Mounith-H/AI-PEGD/images/accuracy_plot_400.png

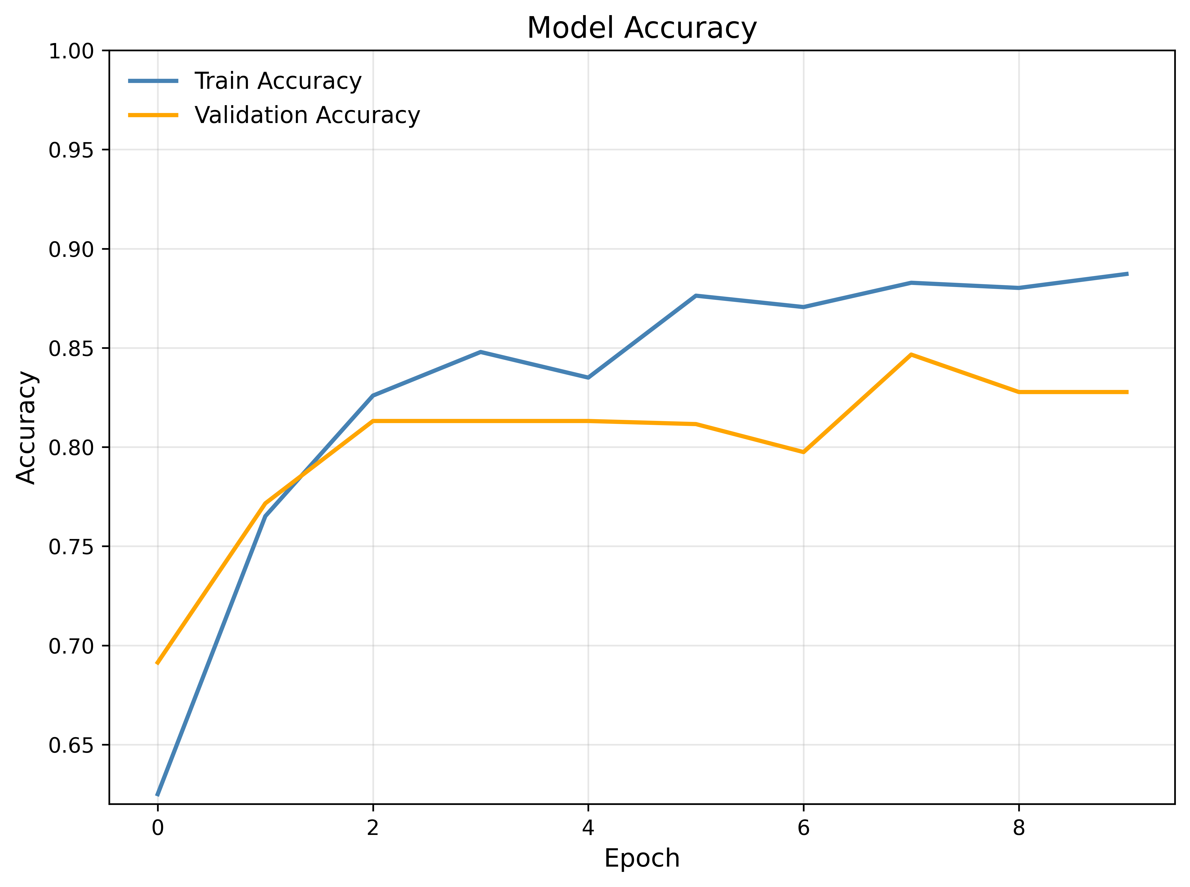
images/accuracy_plot_400.png
