Mounith-H/AI-PEGD/images/accuracy_plot_1000.png

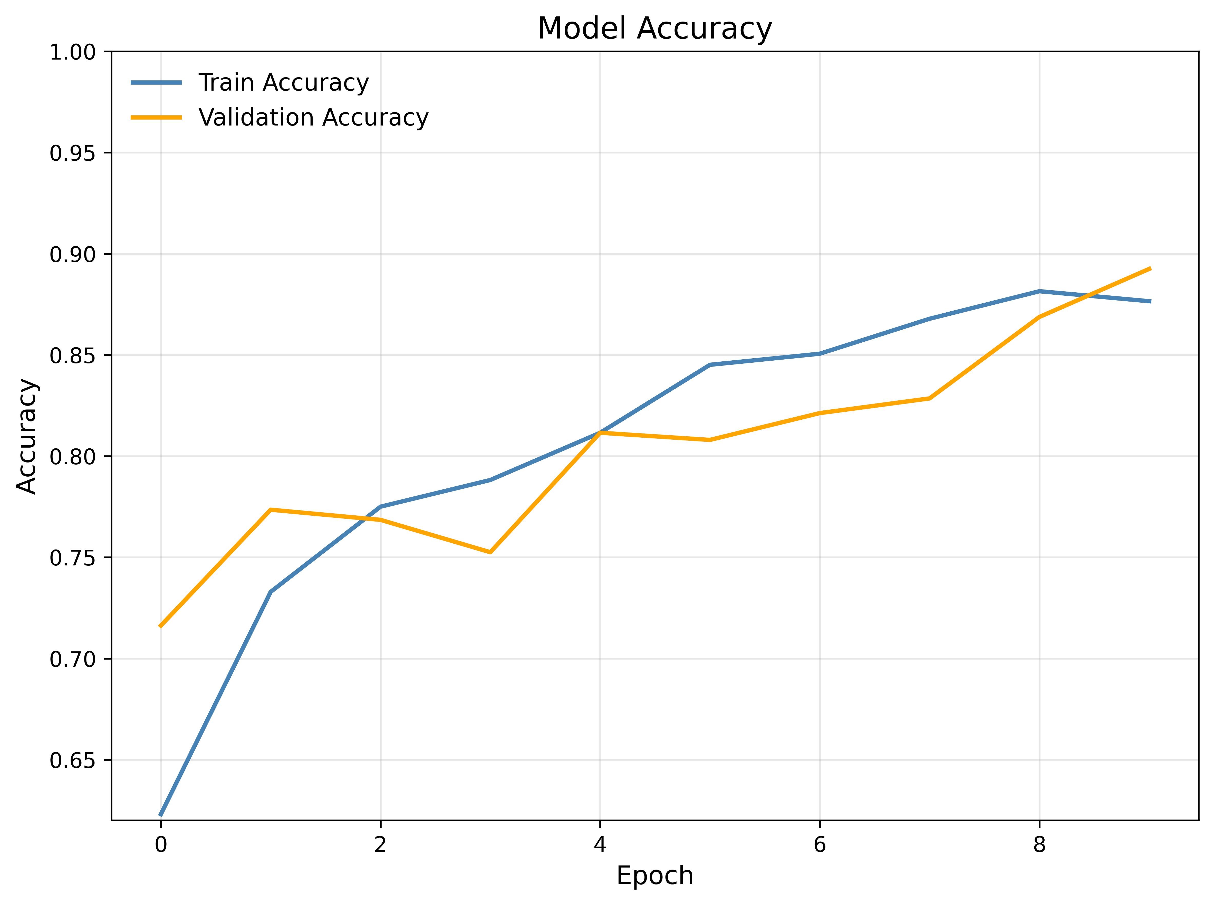
images/accuracy_plot_1000.png
