Mounith-H/AI-PEGD/images/accuracy_plot_1700.png

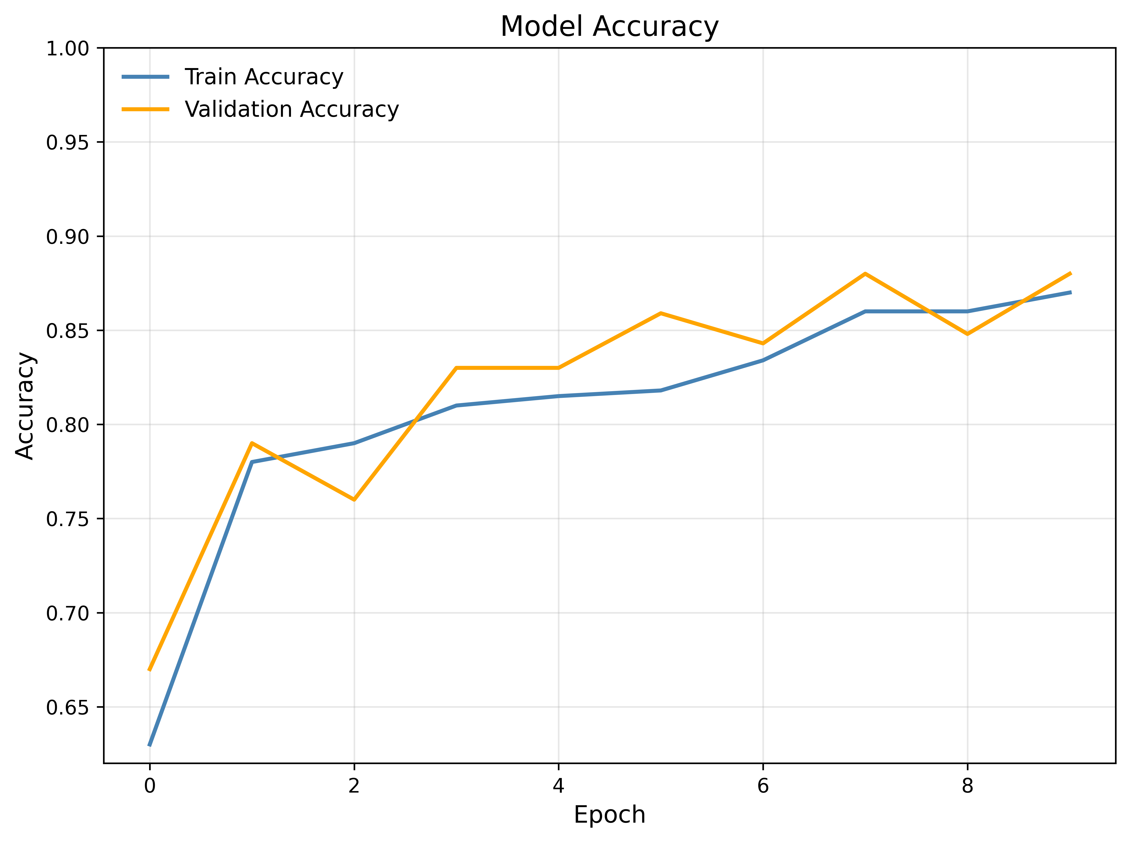
images/accuracy_plot_1700.png
