Mounith-H/AI-PEGD/images/accuracy_plot_2000.png

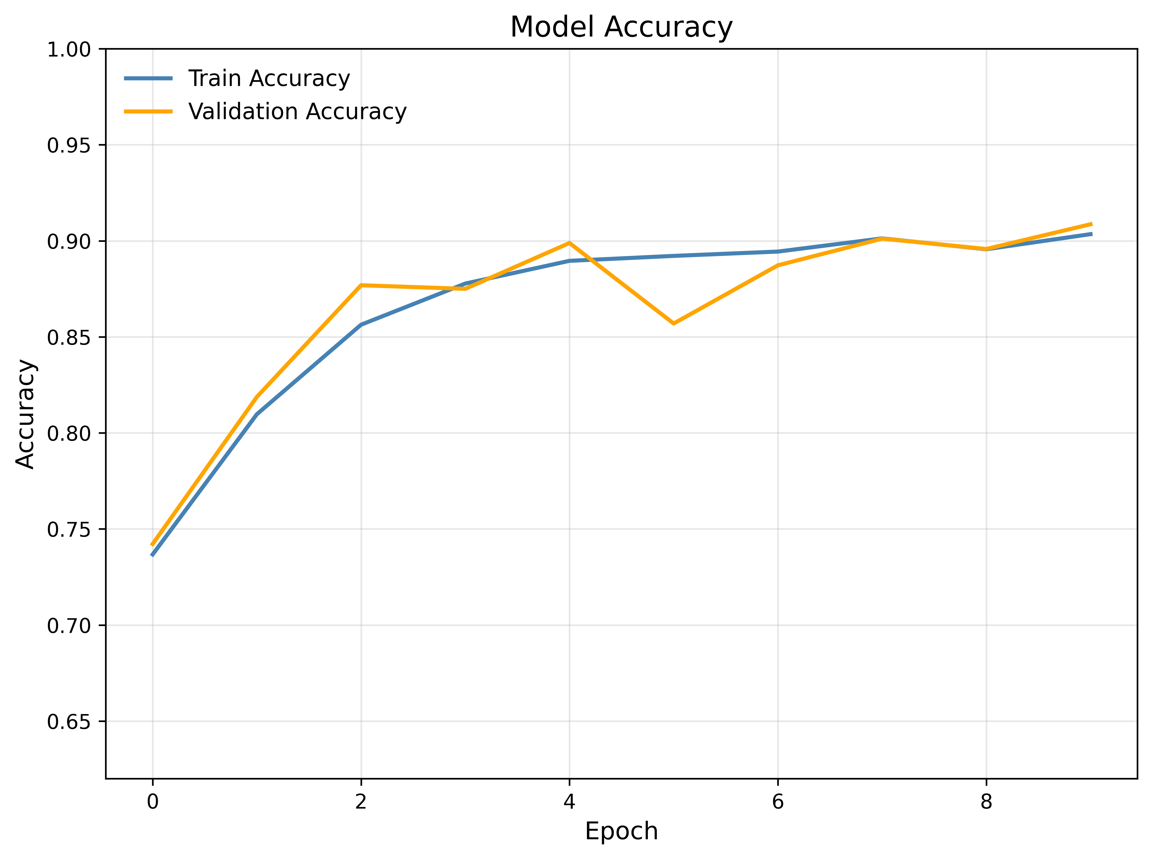
images/accuracy_plot_2000.png
