Mounith-H/AI-PEGD/images/confusion_matrix.jpg

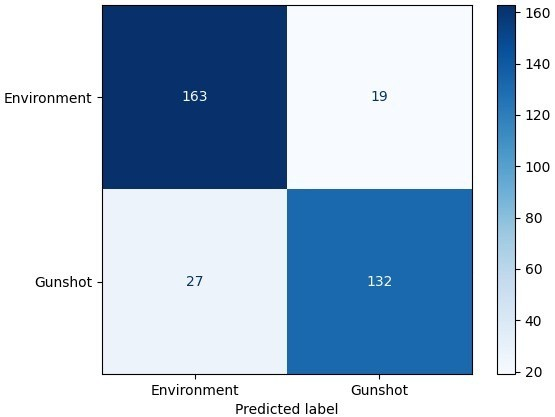
images/confusion_matrix.jpg
