Mounith-H/AI-PEGD/images/flexural_strength.png

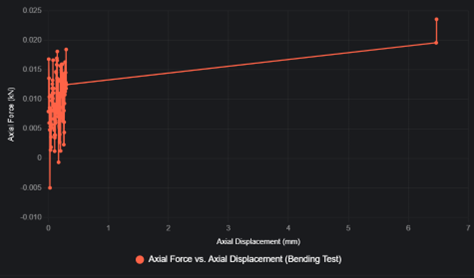
images/flexural_strength.png
