Mounith-H/AI-PEGD/images/flowchat.jpg

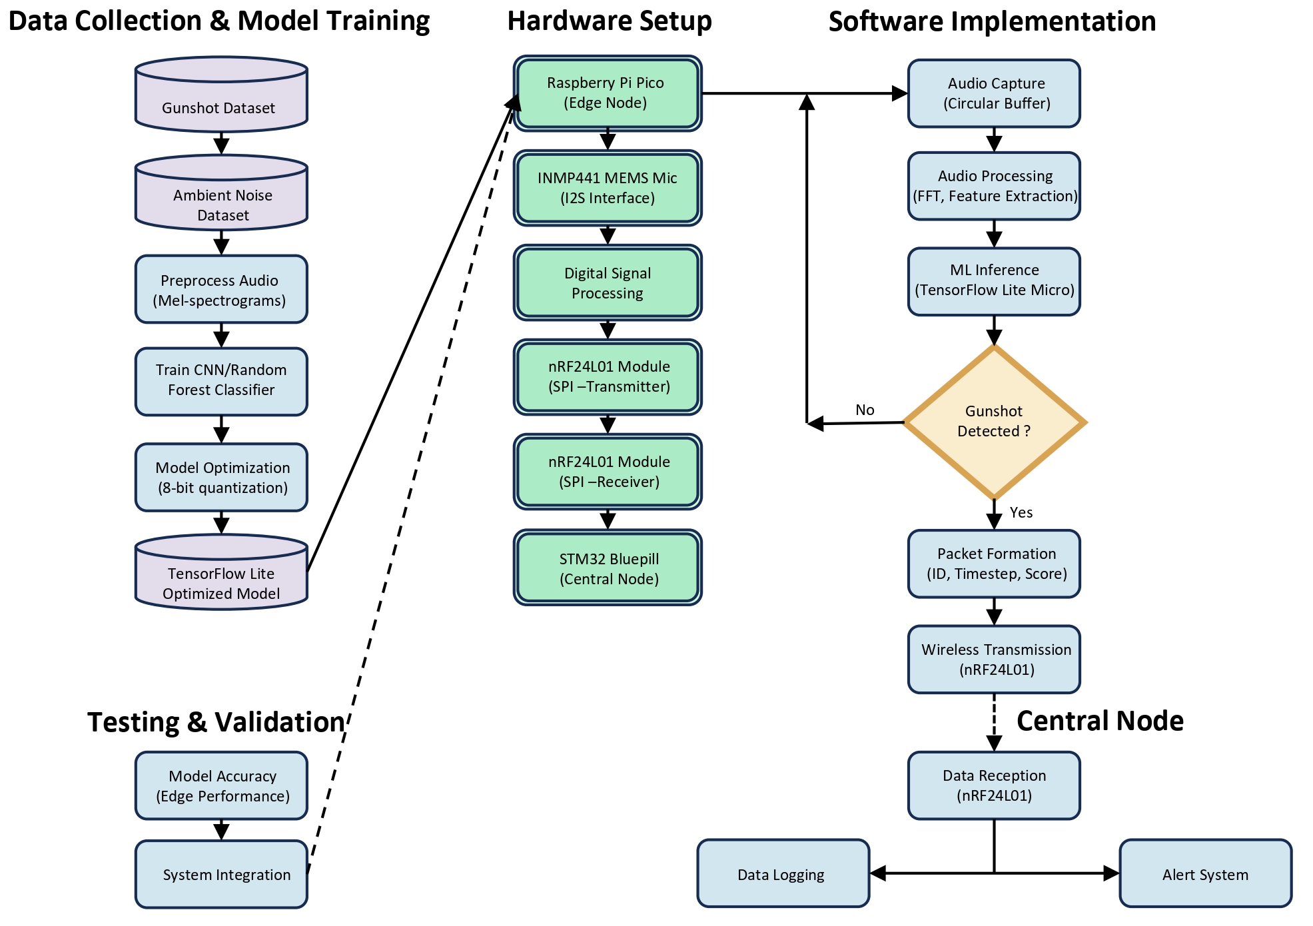
images/flowchat.jpg
