Mounith-H/AI-PEGD/images/loss_plot_1000.png

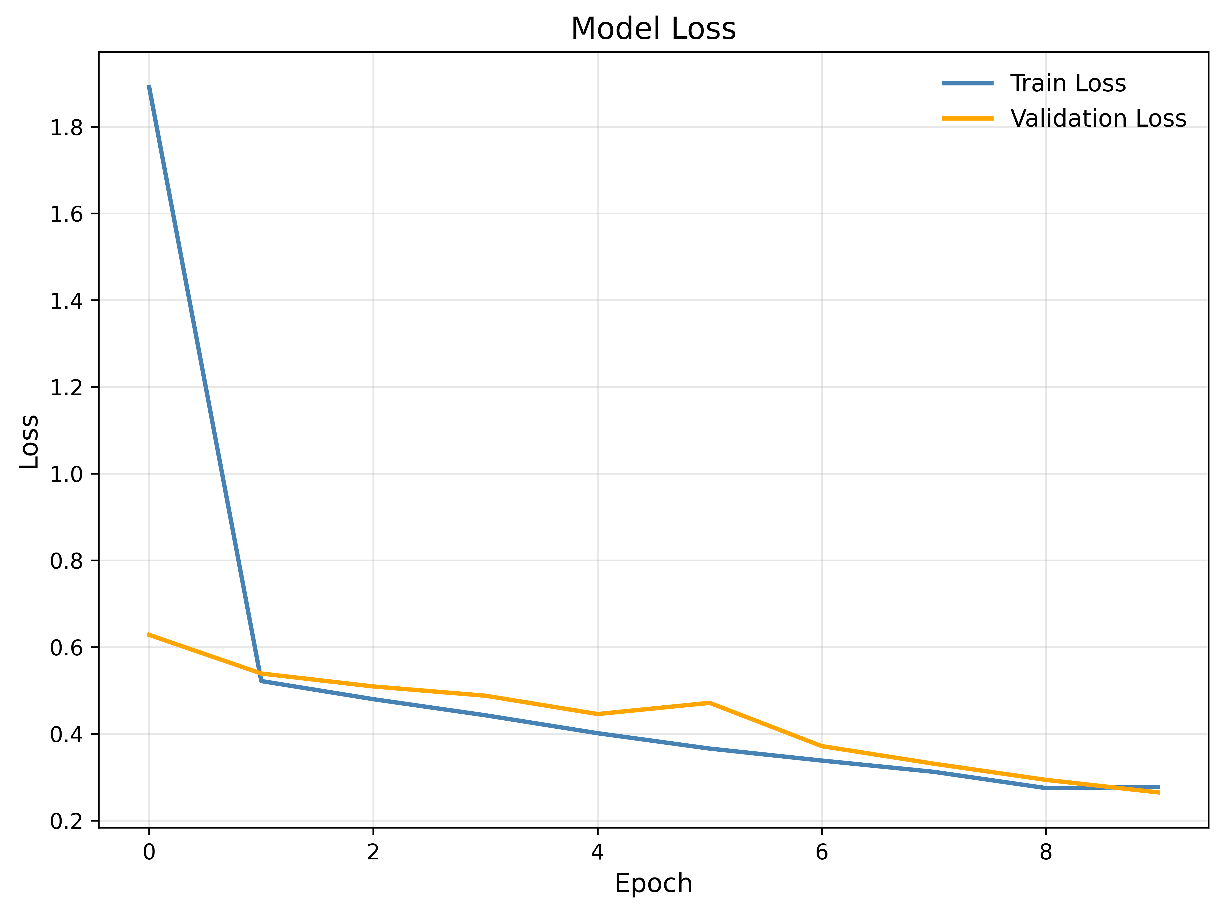
images/loss_plot_1000.png
