Mounith-H/AI-PEGD/images/loss_plot_1700.png

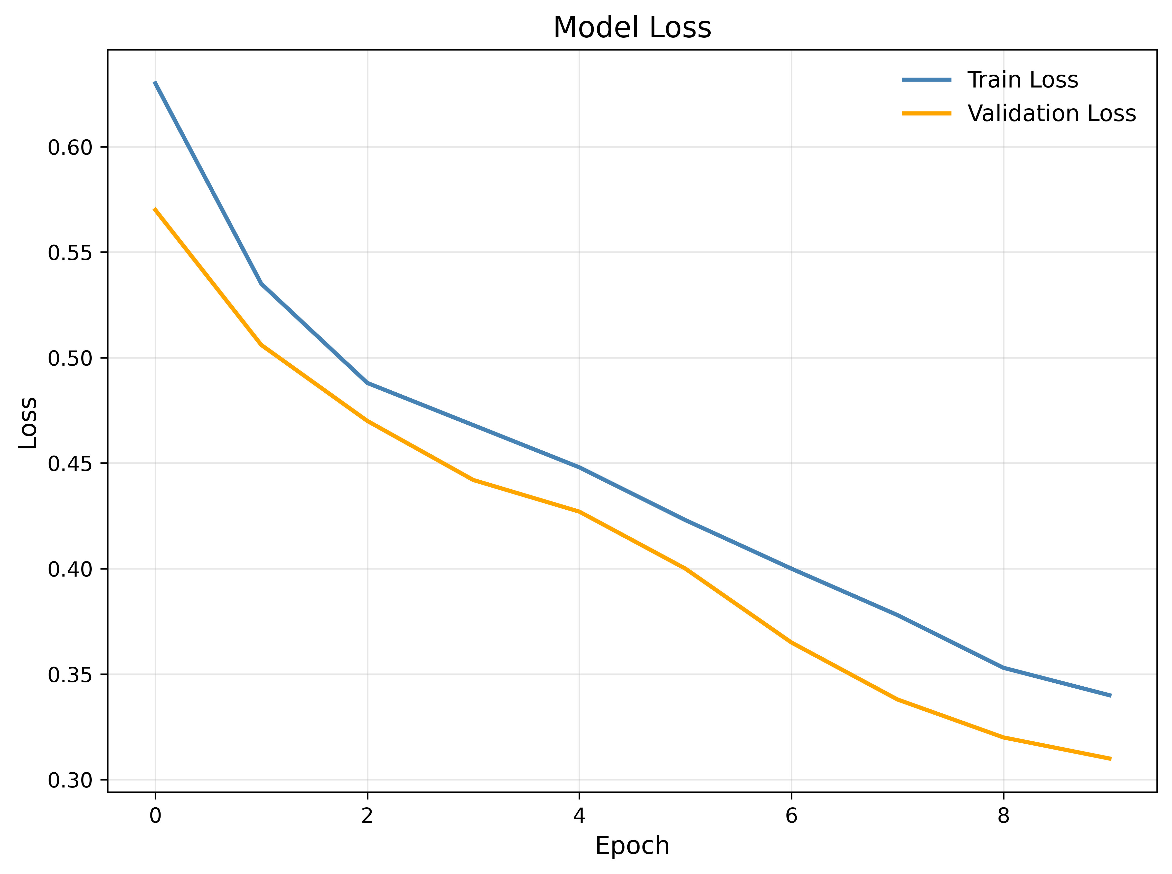
images/loss_plot_1700.png
