Mounith-H/AI-PEGD/images/loss_plot_2000.png

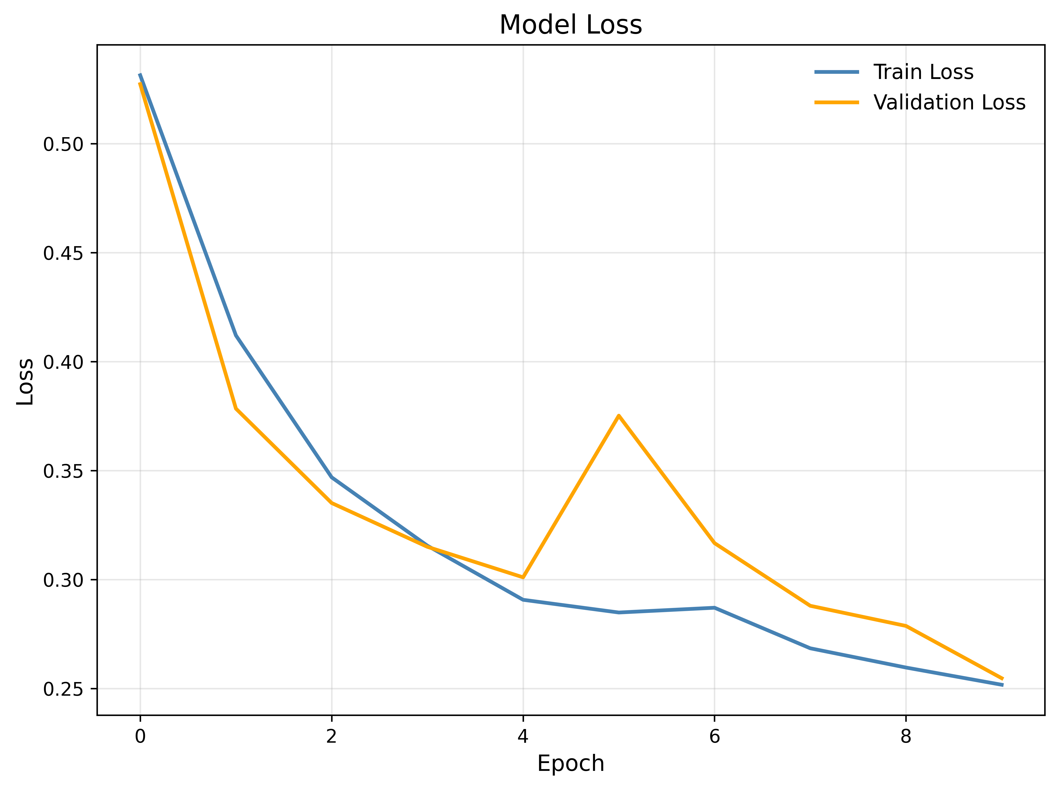
images/loss_plot_2000.png
