Mounith-H/AI-PEGD/images/map_distance.jpeg

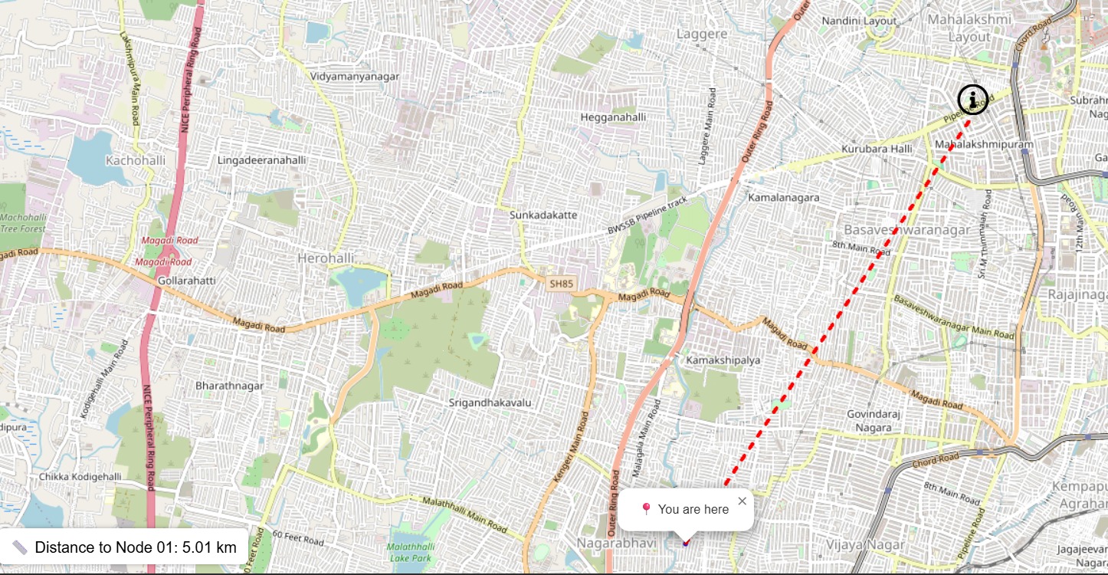
images/map_distance.jpeg
