Mounith-H/AI-PEGD/images/receiver_node.jpg

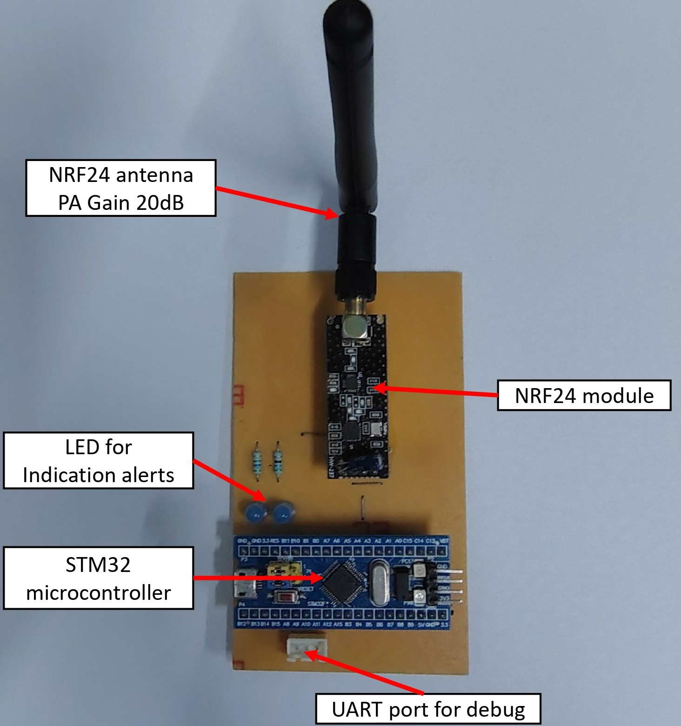
images/receiver_node.jpg
