Mounith-H/AI-PEGD/images/statistics.jpeg

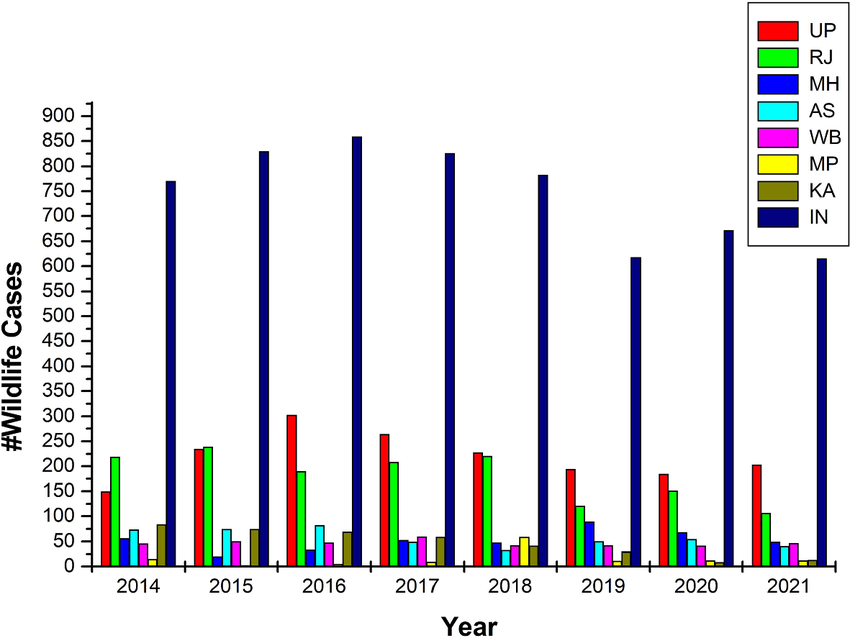
images/statistics.jpeg
