Mounith-H/AI-PEGD/images/Stress_test.jpg

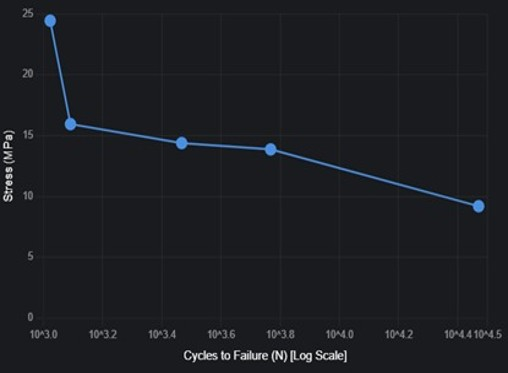
images/Stress_test.jpg
