Mounith-H/AI-PEGD/images/tensile_test.png

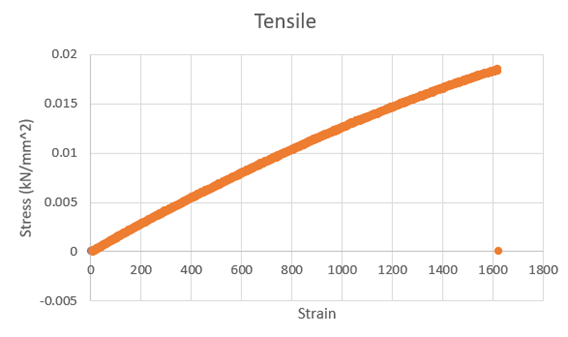
images/tensile_test.png
